rganlath3/PortalGunProjector/VisualDocumentation/CAD-Gameplay_View.png

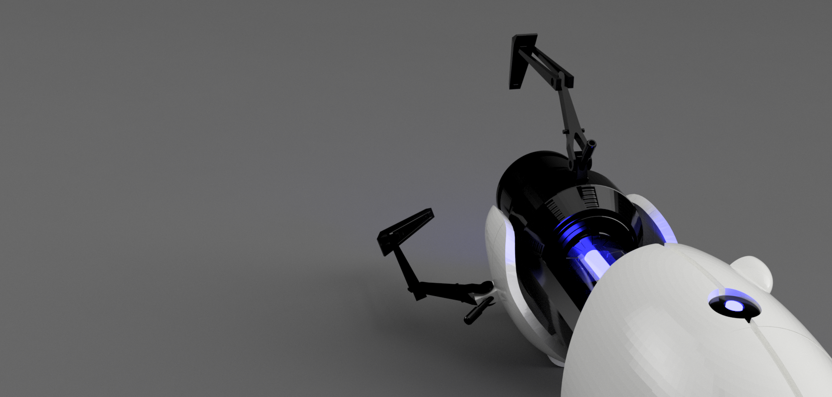
VisualDocumentation/CAD-Gameplay_View.png
